nlohr1/Simple-PWM-Fan-controller_v2/Fotos/IMG_20210415_165335.jpg

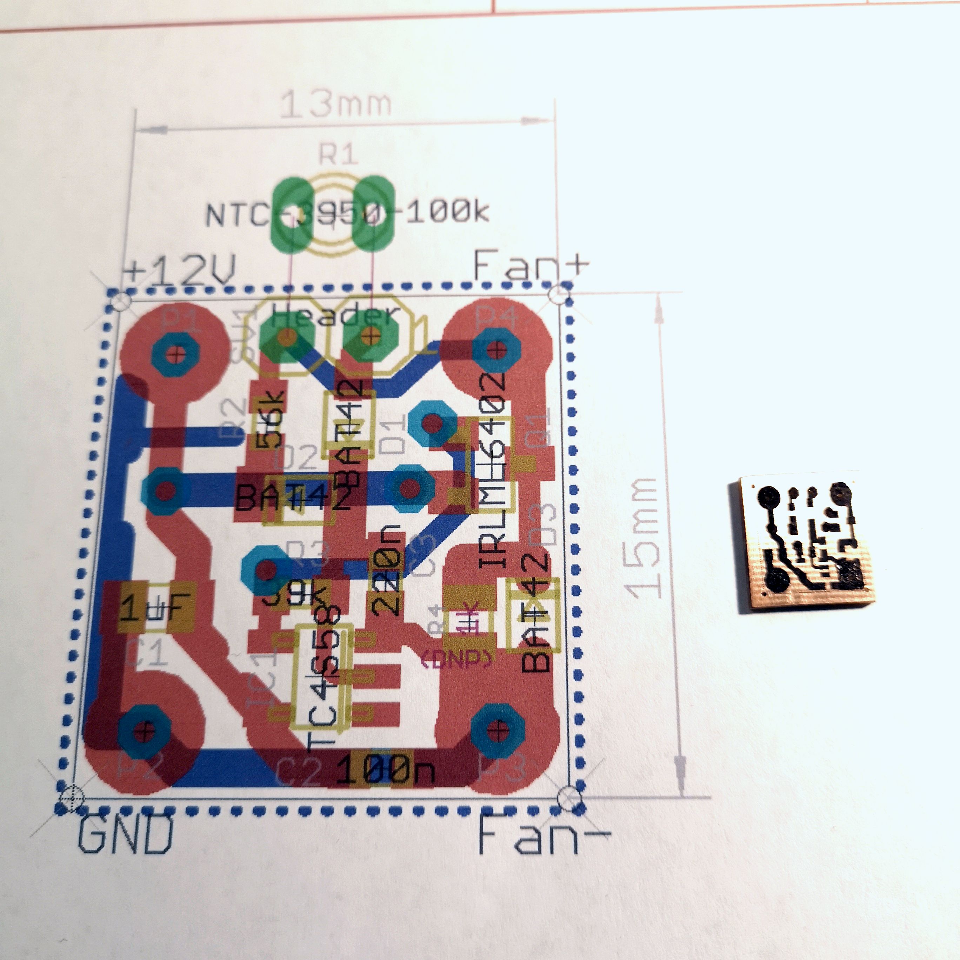
Fotos/IMG_20210415_165335.jpg
