nlohr1/Simple-PWM-Fan-controller_v2/Fotos/IMG_20210415_222720.jpg

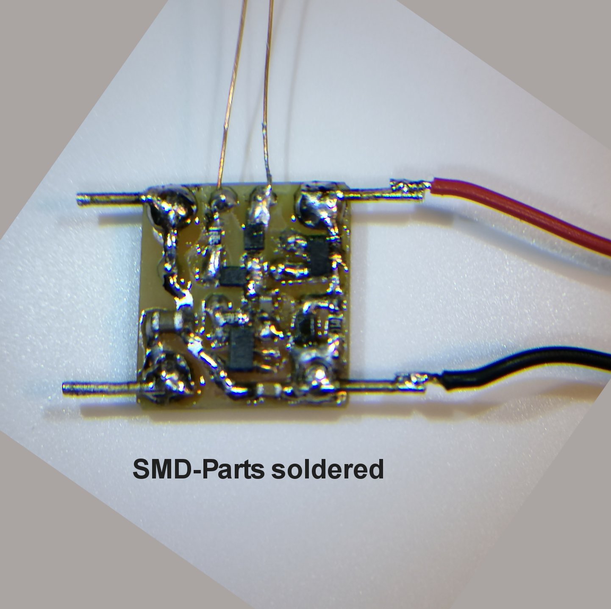
Fotos/IMG_20210415_222720.jpg
